ChapResearch/RoBox/Website/Main/media/birdywords-825x900.png

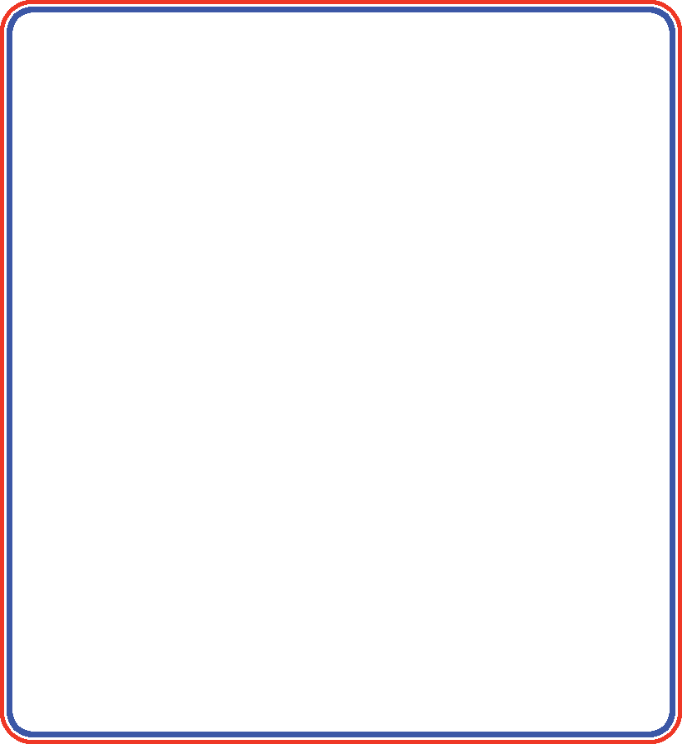
Website/Main/media/birdywords-825x900.png
