ChapResearch/RoBox/hardware/Robot/Production/RomeoMount/Romeo - V7.SLDPRT

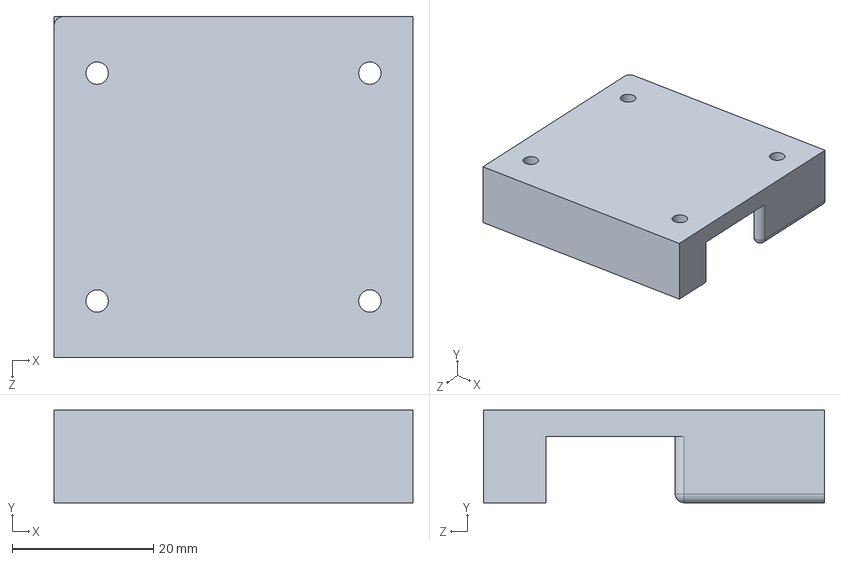
[picture p17: CAD file, 2017-09-03]
hardware/Robot/Production/RomeoMount/Romeo - V7.SLDPRT
50.8 x 13.1 x 48.3 mm
