ChapResearch/RoBox/hardware/Robot/Production/RoofFoam/Roof_Foam.SLDPRT

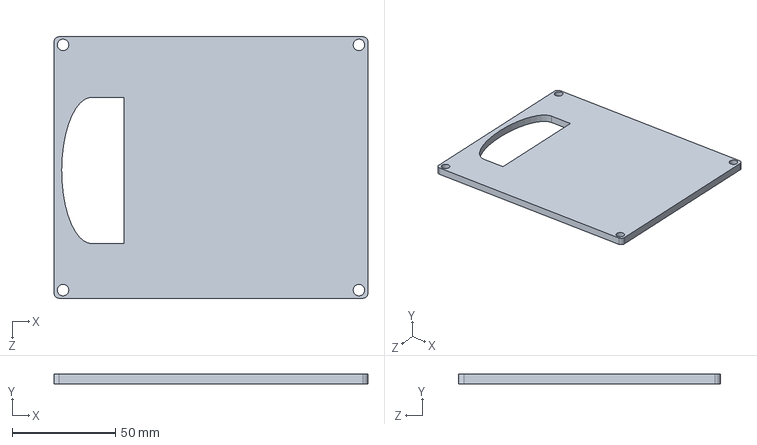
[picture p18: CAD file, 2017-09-03]
hardware/Robot/Production/RoofFoam/Roof_Foam.SLDPRT
152.4 x 4.76 x 127.0 mm
