ChapResearch/RoBox/hardware/Robot/Production/RoofLexan/Roof.SLDPRT

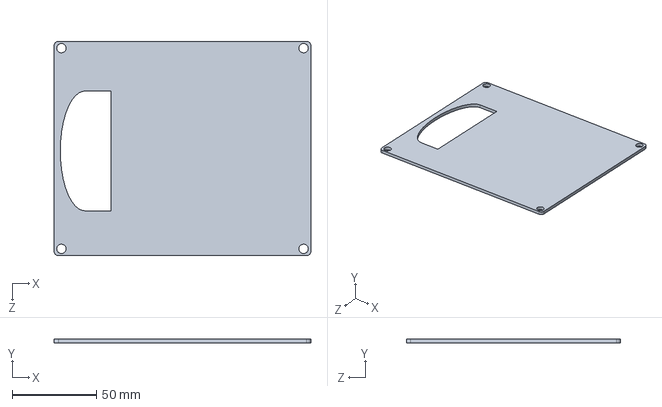
[picture p19: CAD file, 2017-09-03]
hardware/Robot/Production/RoofLexan/Roof.SLDPRT
152.4 x 2.36 x 127.0 mm
