ChapResearch/RoBox/hardware/Robot/Production/SidePlate/Side Plate - V7.SLDPRT

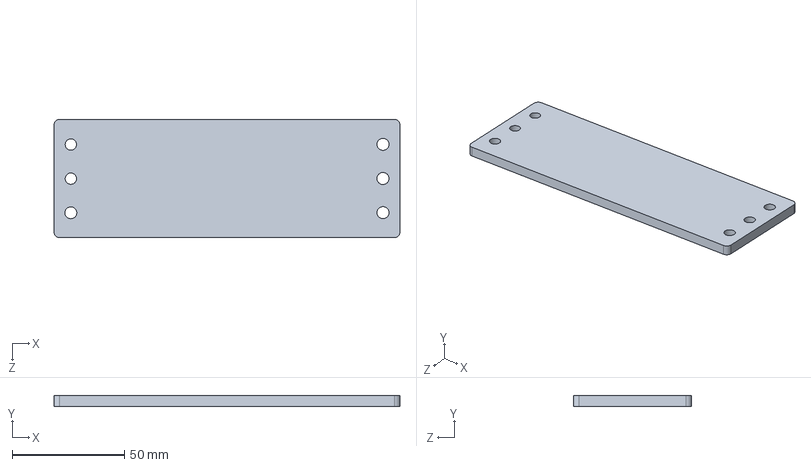
[picture p20: CAD file, 2017-09-03]
hardware/Robot/Production/SidePlate/Side Plate - V7.SLDPRT
154.4 x 4.76 x 52.8 mm
