ChapResearch/RoBox/hardware/Target/ArmConnect/TargetArmConnect v1 (1).amf

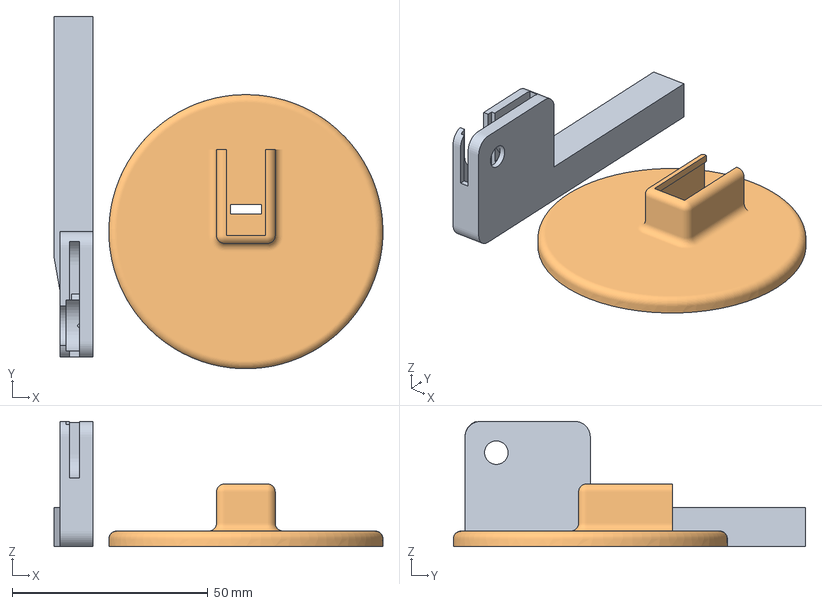
[picture p21: CAD file, 2017-09-03]
hardware/Target/ArmConnect/TargetArmConnect v1 (1).amf
84.0 x 90.0 x 32.0 mm
