ChapResearch/RoBox/hardware/Target/Round/Target Round v1.SLDPRT

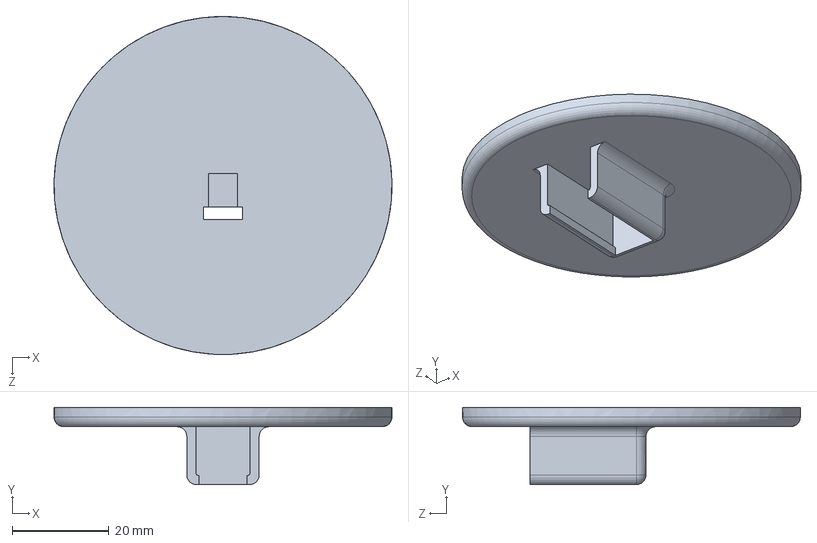
[picture p22: CAD file, 2017-09-03]
hardware/Target/Round/Target Round v1.SLDPRT
70.0 x 16.0 x 70.0 mm
