ChapResearch/RoBox/hardware/Target/Top/Target Top v1.SLDPRT

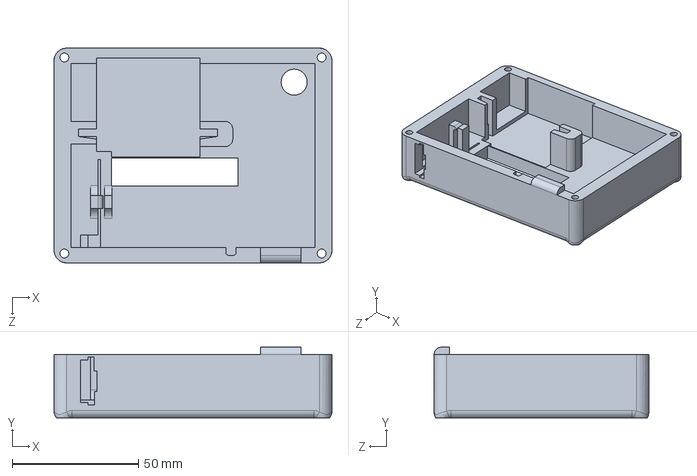
[picture p23: CAD file, 2017-09-03]
hardware/Target/Top/Target Top v1.SLDPRT
110.0 x 28.0 x 85.0 mm
