ChapResearch/RoBox/hardware/Robot/All Versions/Caster/Caster - V10.SLDPRT

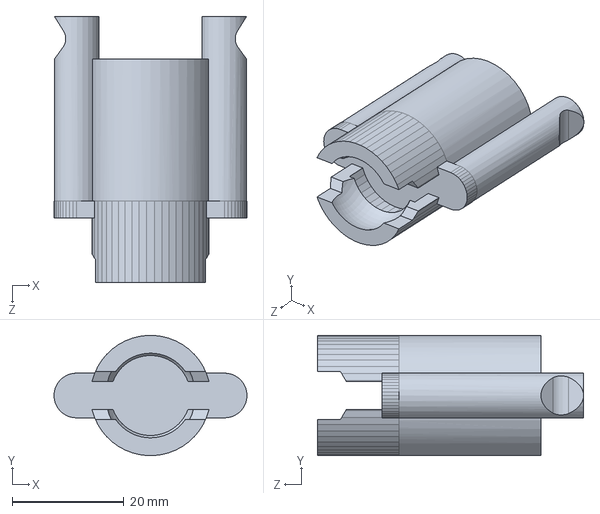
[picture p24: CAD file, 2017-09-03]
hardware/Robot/All Versions/Caster/Caster - V10.SLDPRT
34.5 x 21.5 x 47.6 mm
