ChapResearch/RoBox/hardware/Robot/All Versions/LineFollowMount/Line Follow - V9.SLDPRT

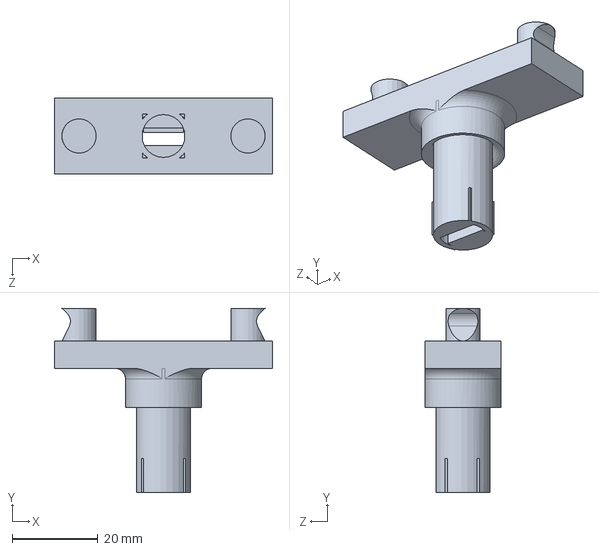
[picture p25: CAD file, 2017-09-03]
hardware/Robot/All Versions/LineFollowMount/Line Follow - V9.SLDPRT
50.8 x 43.0 x 17.7 mm
