ChapResearch/RoBox/hardware/Robot/All Versions/Plates/Chassis - V10.SLDPRT

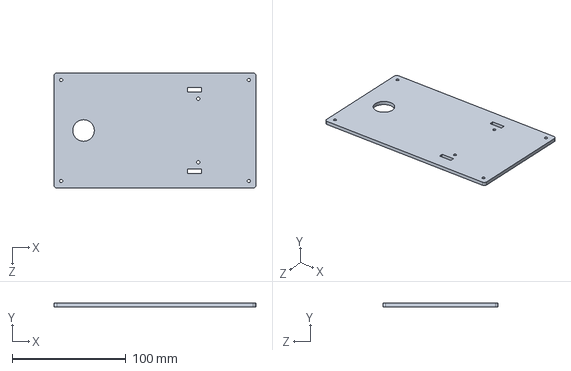
[picture p26: CAD file, 2017-09-03]
hardware/Robot/All Versions/Plates/Chassis - V10.SLDPRT
177.8 x 3.17 x 101.6 mm
