ChapResearch/RoBox/hardware/Robot/All Versions/RomeoMount/Romeo - V7.SLDPRT

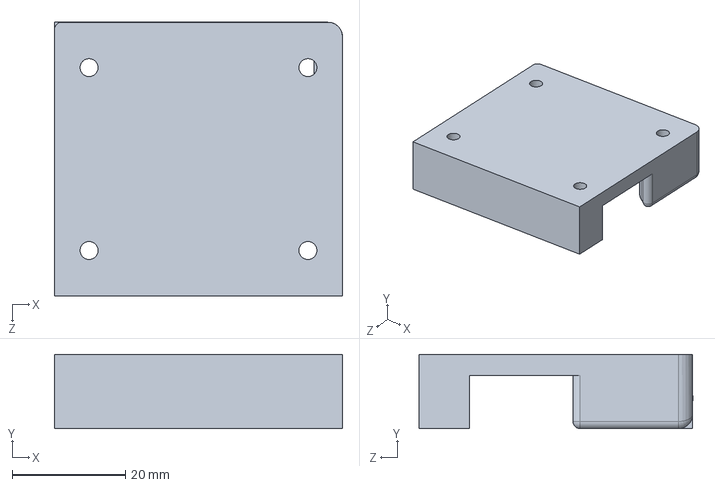
[picture p27: CAD file, 2017-09-03]
hardware/Robot/All Versions/RomeoMount/Romeo - V7.SLDPRT
50.8 x 13.1 x 48.3 mm
