ChapResearch/RoBox/hardware/Target/ArmConnect/TargetArmConnect v1.SLDPRT

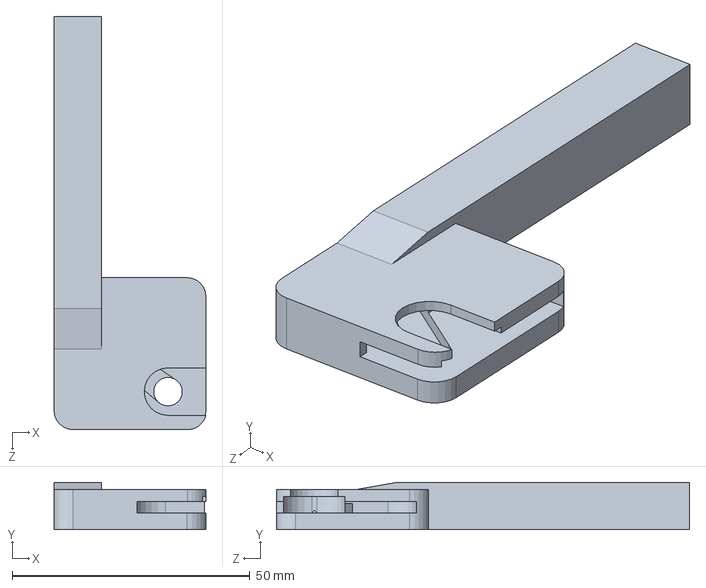
[picture p28: CAD file, 2017-09-03]
hardware/Target/ArmConnect/TargetArmConnect v1.SLDPRT
32.0 x 10.0 x 87.0 mm
