ChapResearch/RoBox/hardware/Target/Base/Target Base v2.SLDPRT

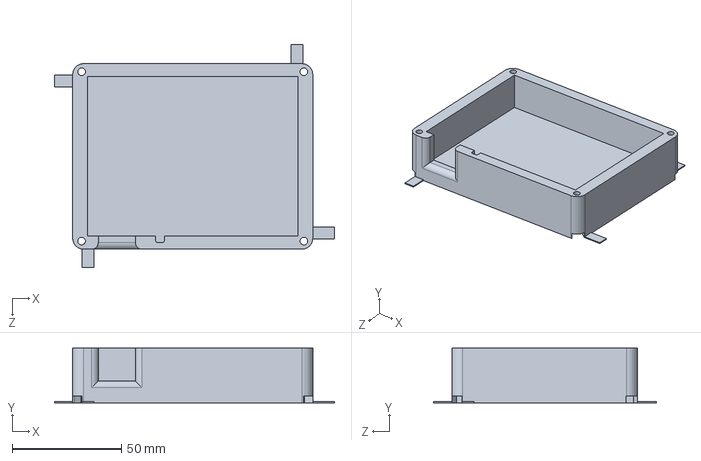
[picture p29: CAD file, 2017-09-03]
hardware/Target/Base/Target Base v2.SLDPRT
128.2 x 25.0 x 102.0 mm
