ChapResearch/RoBox/firmware/drivers/RoBoxBLENanoV11/roboxDrivers.h

//
// RoBoxBLENanoV11.h
//
//   The include file that you should use to include all of the
//   RoBox  driver files for this BLE-Nano board.
//
#include "roboxIR.h"
#include "roboxTone.h"
#include "roboxUltra.h"
#include "roboxMotor.h"
#include "roboxLED.h"
#include "roboxLineFollow.h"
#include "roboxBLE.h"
#include "roboxServo.h"
