ChapResearch/RoBox/firmware/RoBox/hardware.h

//
// hardware.h
//
//    Definitions of the hardware.  The code ALWAYS calls these. But they are
//    defined based upon the type of hw platform, including SIMULATION as
//    defined in the Makefile. Each of the REAL hardware files needs to implement
//    these functions.  See the Makefile for instructions to use different hardware.
//

void hw_init();                         // initializes all the hardware
unsigned int hw_readLineFollow();	// returns an int between 0 and 100
unsigned int hw_readUltraSonic();	// returns between 0 and 100 (cm)
uint32_t hw_readIR();			// checks IR for incoming "hit", returns it if so (may use 2 sensors)
void hw_motor(char,int);		// sets 'L' or 'R' motor to power between -100 and 100
void hw_motorReverse(char);		// sets either 'L' or 'R' motor to "reverse" mode
void hw_servoShoot();                   // shoots the ball by positioning the servo
void hw_servoLoad();                    // loads the ball by positioning the servo
void hw_servoStart();                   // starts rotating the servo
void hw_servoStop();                    // stops rotating the servo
void hw_blaster(uint8_t,int,int);	// sends out <count> blasts at <power>
void hw_led(int,int);			// turns on/off/blink LED number X
void hw_tone(int,int);			// turns on tone <freq> for <dur> ms
void hw_update();			// updates all actions - called at end of loop
void hw_bleStart();			// get BLE up and running
int  hw_bleReceive();			// receive a byte from BLE (-1 if non available)
void hw_bleSend(byte*,int);		// sends an output buffer (bytes) to BLE
const char *hw_getname();		// get the BLE name
void hw_setname(const char *);		// set the BLE name
