ChapResearch/RoBox/firmware/drivers/RoBoxBLENanoV11/roboxLED.h

//
// roboxLED.h
//

#ifndef ROBOXLED_H
#define ROBOXLED_H

class LED {
 private:
  int		led;
  int		state;
  int 		blink_ms;
  unsigned long blink_target;
  
 public: 
  LED(int);
  void On();
  void Off();
  void Toggle();
  void Blink(int);
  void Update();	
};
#endif
