ChapResearch/RoBox/firmware/RoBox/program.cpp

//
// program.cpp
//
//   Implements a "program" allowing the virtual machine to
//   process it effeciently.  For debugging, the program is
//   kept in memory, but on the Robox, it will be in EEPROM.
//

#include "Arduino.h"
#include "program.h"
#include "EEPROM.h"

#ifdef DEBUGGING
#include <malloc.h>
#include <string.h>
#include <stdio.h>
#endif

Program::Program()
{
	base = 0;
	ptr = 0;
	size = 0;
	baseEnd = base + size;
	last_if_value = true;	// an out-of-place stand-alone else will never execute with this init

}

Program::Program(int EEPROM_base, int count)
{
	base = EEPROM_base;
	ptr = 0;
	size = count;
	baseEnd = base + size;
	last_if_value = true;	// an out-of-place stand-alone else will never execute with this init
}

Program::Program(int count, const char *prog)
{
	base = 0;
	ptr = 0;
	size = count;
	baseEnd = base + size;

	for(int i=ptr; i < size; i++) {
		EEPROM.write(i,(byte)prog[i]);
	}

	last_if_value = true;	// an out-of-place stand-alone else will never execute with this init
}

//
// This constructor takes a "sub-program" view of an existing program.
//
Program::Program(Program prog, int start, int endExclusive)
{
    base = start;
    ptr = 0;
    size = endExclusive - start;
    baseEnd = base+size;

    last_if_value = true;	// an out-of-place stand-alone else will never execute with this init
}
	

//
// Skip() - skips over the next COUNT characters, normally used to skip sub-program
//
void Program::Skip(int count)
{
  ptr += count;
}

char Program::Next()
{
	if(ptr >= size) {
		return(0);	// zero is returned continuously if at th end of the program
	}
	byte r = EEPROM.read(base+ptr);
	ptr++;
	return(r);
}

int Program::Position()
{
    return(base+ptr);
}

bool Program::AtEnd()
{
	return(ptr >= size);
}	

int Program::Index()
{
	return(ptr);
}

void Program::SetIndex(int newptr)
{
	ptr = newptr;
}

void Program::Reset()
{
	SetIndex(0);
	last_if_value = true;
}
