ChapResearch/RoBox/firmware/RoBox/program.h

//
// program.h
//

#ifndef PROGRAM_H
#define PROGRAM_H

class Program {
private:
	int	base;		// a pointer into EEPROM where the program starts
	int	ptr;		// a pointer into the program
	int	baseEnd;	// base+size - lowers the number of adds we need to do!
public:
	int	size;		// size of the program
	Program();
	Program(int,int);		// standard load of pre-loaded EEPROM as program
	Program(int,const char *);
	Program(Program,int,int);
	void Dump();
	void Dump(int);
	char Next();		// shifts from byte (unsigned char) to char to get sign extension
	int Index();
	void SetIndex(int);
	void Reset();
	bool AtEnd();
	void Skip(int);
	int Position();

        // each program stores the value of the last If expression evaluation - it is used for
        // the "else".  NOTE that if an else isn't right next to an If, then the else
        // will STILL take the last If expression evalution no matter where it occured.
	// It is always defaulted to "true" so a stand-alone else won't execute

	int	last_if_value;	
};

#endif
